genneth/Glider/fw/User/config.c

//
// Grimoire
// Copyright 2025 Wenting Zhang
//
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
#include "platform.h"
#include "board.h"
#include "app.h" 

config_t config;

void config_init(void) {
    // Set default values
    config.size_x_mm = 270;
    config.size_y_mm = 203;
    config.mfg_week = 1;
    config.mfg_year = 0x20;

    // 1600x1200 @ 60
//    config.pclk_hz = 162000000;
//    config.hact = 1600;
//    config.vact = 1200;
//    config.hblk = 560;
//    config.hfp = 64;
//    config.hsync = 192;
//    config.vblk = 50;
//    config.vfp = 1;
//    config.vsync = 3;
//    config.tcon_vfp = 45;
//    config.tcon_vsync = 1;
//    config.tcon_vbp = 2;
//    config.tcon_vact = 1200;
//    config.tcon_hfp = 120;
//    config.tcon_hsync = 10;
//    config.tcon_hbp = 10;
//    config.tcon_hact = 400;

    // 1600x1200 @ 75
//    config.pclk_hz = 156618000;
//    config.hact = 1600;
//    config.vact = 1200;
//    config.hblk = 80;
//    config.hfp = 8;
//    config.hsync = 32;
//    config.vblk = 43;
//    config.vfp = 29;
//    config.vsync = 8;
//
//    config.tcon_vfp = 11;
//    config.tcon_vsync = 1;
//    config.tcon_vbp = 2;
//    config.tcon_vact = 1200;
//    // HFP + HSYNC + HBP = Incoming HBLK / 4
//    config.tcon_hfp = 16;
//    config.tcon_hsync = 2;
//    config.tcon_hbp = 2;
//    config.tcon_hact = 400;


    // 1448x1072 @ 75
    // config.pclk_hz = 127320000;
    // config.hact = 1448;
    // config.vact = 1072;
    // config.hblk = 80;
    // config.hfp = 8;
    // config.hsync = 32;
    // config.vblk = 39;
    // config.vfp = 25;
    // config.vsync = 8;

    // config.tcon_vfp = 11;
    // config.tcon_vsync = 1;
    // config.tcon_vbp = 2;
    // config.tcon_vact = 1072;
    // // HFP + HSYNC + HBP = Incoming HBLK / 4
    // config.tcon_hfp = 17;
    // config.tcon_hsync = 2;
    // config.tcon_hbp = 1;
    // config.tcon_hact = 362;

//    config.pclk_hz = 72509000;
//    config.hact = 1040;
//    config.vact = 1040;
//    config.hblk = 80;
//    config.hfp = 8;
//    config.hsync = 32;
//    config.vblk = 39;
//    config.vfp = 25;
//    config.vsync = 8;
//
//    config.tcon_vfp = 11;
//    config.tcon_vsync = 1;
//    config.tcon_vbp = 2;
//    config.tcon_vact = 1040;
//    // HFP + HSYNC + HBP = Incoming HBLK / 4
//    config.tcon_hfp = 17;
//    config.tcon_hsync = 2;
//    config.tcon_hbp = 1;
//    config.tcon_hact = 260;

//    config.pclk_hz = 162000000;
//    config.hact = 1872;
//    config.vact = 1404;
//    config.hblk = 40;
//    config.hfp = 8;
//    config.hsync = 16;
//    config.vblk = 6;
//    config.vfp = 2;
//    config.vsync = 2;
//
//    config.tcon_vfp = 1;
//    config.tcon_vsync = 1;
//    config.tcon_vbp = 2;
//    config.tcon_vact = 1404;
//    // HFP + HSYNC + HBP = Incoming HBLK / 4
//    config.tcon_hfp = 7;
//    config.tcon_hsync = 2;
//    config.tcon_hbp = 1;
//    config.tcon_hact = 468;
//
//    config.vcom = -2.17f;
//    config.vgh = 22.0f;
//
//    config.mirror = 0;

    // 2232x1680 @ 40
//    config.pclk_hz = 158873000;
//    config.hact = 2240;
//    config.vact = 1680;
//    config.hblk = 80;
//    config.hfp = 8;
//    config.hsync = 32;
//    config.vblk = 32;
//    config.vfp = 18;
//    config.vsync = 8;
//
//    config.tcon_vfp = 12;
//    config.tcon_vsync = 1;
//    config.tcon_vbp = 1;
//    config.tcon_vact = 1680;
//    // HFP + HSYNC + HBP = Incoming HBLK / 4
//    config.tcon_hfp = 16;
//    config.tcon_hsync = 2;
//    config.tcon_hbp = 2;
//    config.tcon_hact = 560;
//
//    config.vcom = -0.8f;
//    config.vgh = 22.0f;

    // 2200x1648 @ 42
//    config.pclk_hz = 160972000;
//    config.hact = 2200;
//    config.vact = 1648;
//    config.hblk = 80;
//    config.hfp = 8;
//    config.hsync = 32;
//    config.vblk = 33;
//    config.vfp = 19;
//    config.vsync = 8;
//
//    config.tcon_vfp = 11;
//    config.tcon_vsync = 1;
//    config.tcon_vbp = 2;
//    config.tcon_vact = 1648;
//    config.tcon_hfp = 16;
//    config.tcon_hsync = 2;
//    config.tcon_hbp = 2;
//    config.tcon_hact = 550;

//    config.pclk_hz = 51500000;
//    config.hact = 800;
//    config.vact = 480;
//    config.hblk = 80;
//    config.hfp = 8;
//    config.hsync = 32;
//    config.vblk = 8;
//    config.vfp = 2;
//    config.vsync = 2;
//
//    config.tcon_vfp = 4;
//    config.tcon_vsync = 1;
//    config.tcon_vbp = 2;
//    config.tcon_vact = 480;
//    config.tcon_hfp = 4;
//    config.tcon_hsync = 4;
//    config.tcon_hbp = 12;
//    config.tcon_hact = 200;

    config.vcom = -2.30f;
    config.vgh = 25.0f;

    //config.mirror = 1;

    config.input_sel = INPUT_SEL_AUTO;
}

void config_load(void) {
    SPIFFS_clearerr(&spiffs_fs);
    spiffs_file f = SPIFFS_open(&spiffs_fs, "config.bin", SPIFFS_O_RDONLY, 0);
    if (SPIFFS_errno(&spiffs_fs) != 0)
        return;
    
    spiffs_stat s;
    SPIFFS_fstat(&spiffs_fs, f, &s);
    uint32_t size = s.size;
    if (size != sizeof(config)) {
        SPIFFS_close(&spiffs_fs, f);
        return;
    }

    SPIFFS_read(&spiffs_fs, f, &config, sizeof(config));
    SPIFFS_close(&spiffs_fs, f);
}

void config_save(void) {
    SPIFFS_clearerr(&spiffs_fs);
    spiffs_file f = SPIFFS_open(&spiffs_fs, "config.bin", SPIFFS_O_CREAT | SPIFFS_O_TRUNC | SPIFFS_O_WRONLY, 0);
    if (SPIFFS_errno(&spiffs_fs) != 0)
        return;
    
    SPIFFS_write(&spiffs_fs, f, &config, sizeof(config));
}
